richardhawthorn/Wifi14Segment-smd/images/DSC_5023.JPG

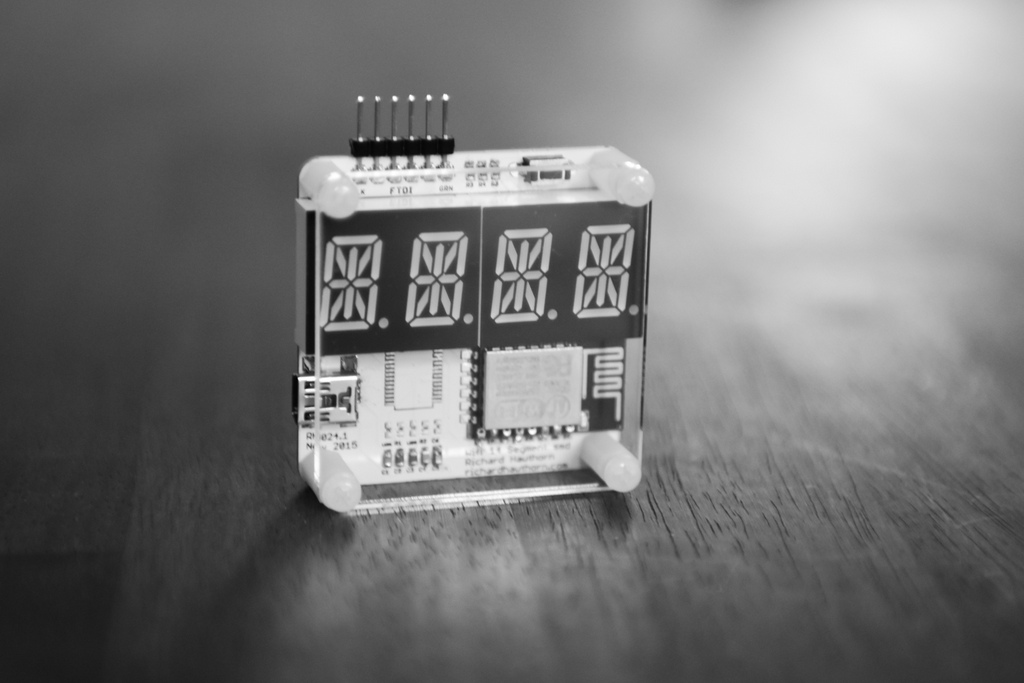
images/DSC_5023.JPG
