richardhawthorn/Wifi14Segment-smd/images/DSC_5024.JPG

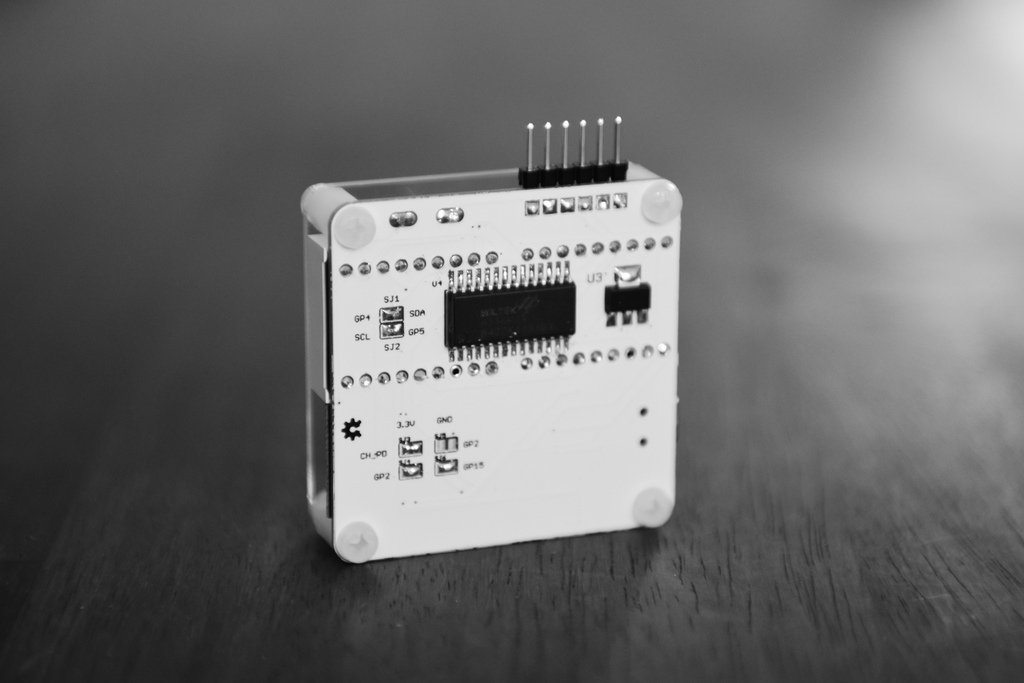
images/DSC_5024.JPG
